joebowen/arduino_altimeter/Schematic&Boards/Joe's NonPyro Altimeter/Finished/arduino_schematic_with_ADXL377_without_pyro_etch_copper_bottom.pdf

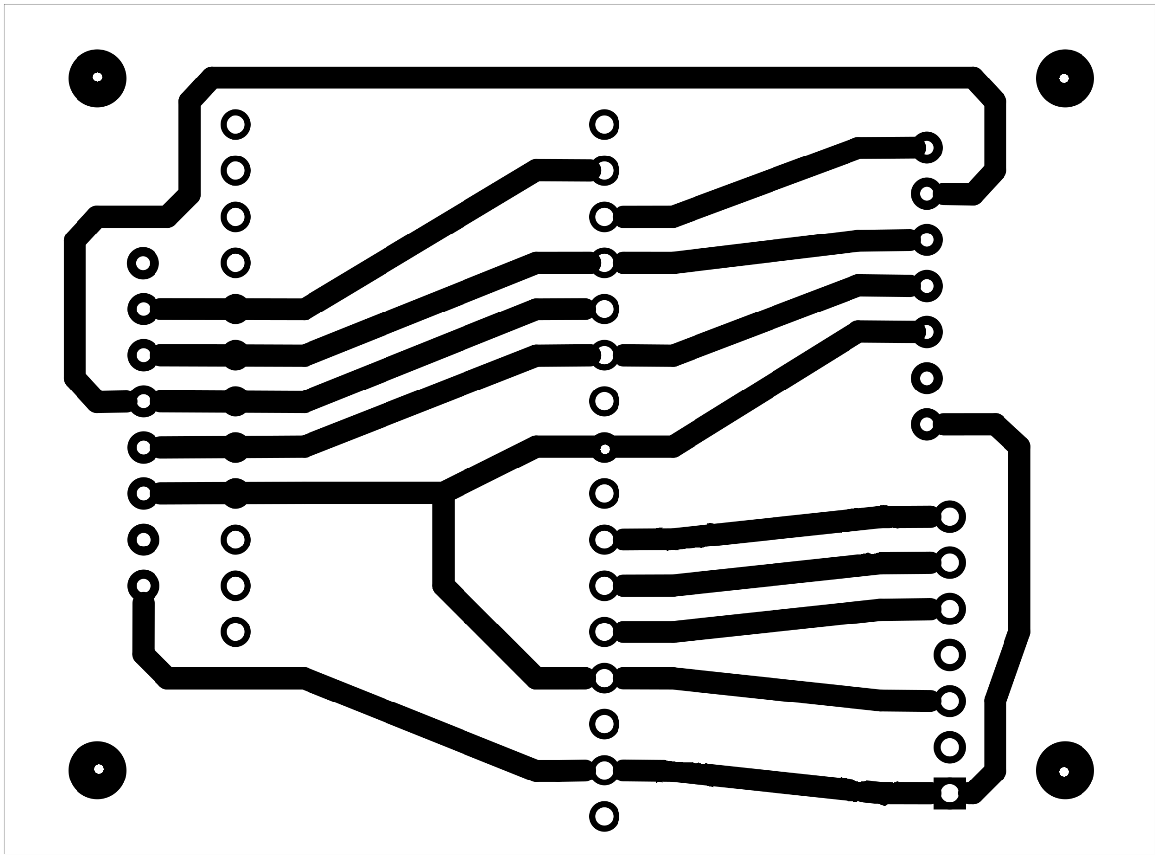
[picture p1: page 1]
