joebowen/arduino_altimeter/Schematic&Boards/Dan's Altimeter/arduino_schematic_etch_silk_bottom.pdf

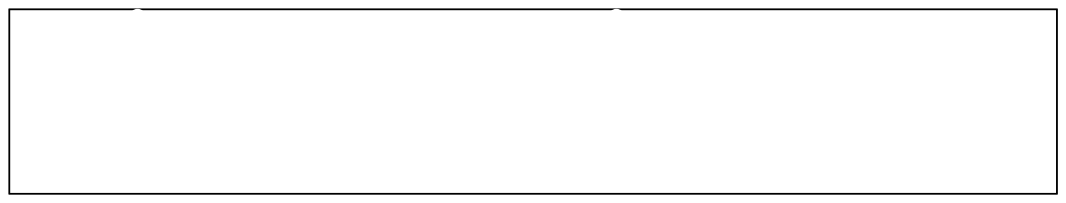
[picture p13: page 1]
