joebowen/arduino_altimeter/Schematic&Boards/Dan's Altimeter/arduino_schematic_etch_silk_bottom_mirror.pdf

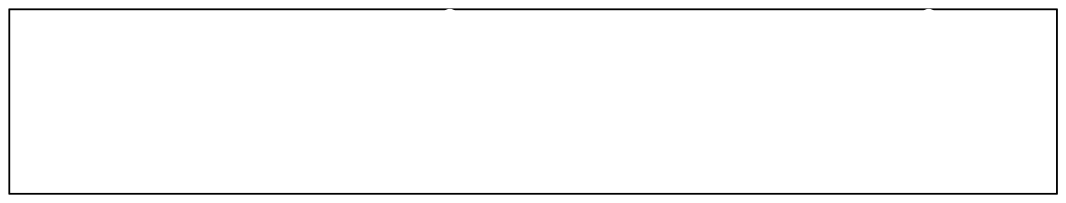
[picture p14: page 1]
