joebowen/arduino_altimeter/Schematic&Boards/Dan's Altimeter/arduino_schematic_etch_silk_top.pdf

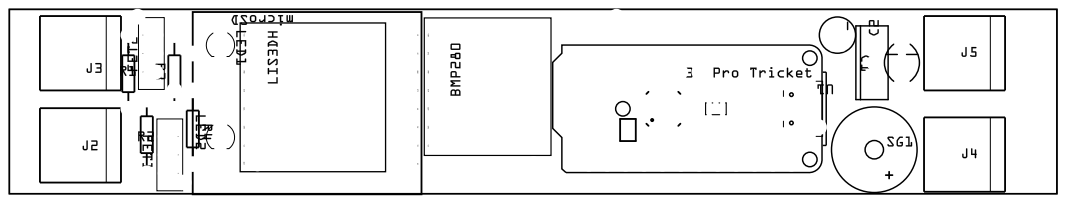
[picture p15: page 1]
