joebowen/arduino_altimeter/Schematic&Boards/Dan's Altimeter/arduino_schematic_etch_silk_top_mirror.pdf

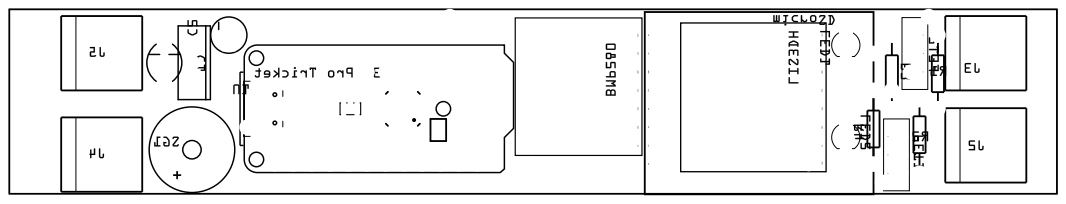
[picture p16: page 1]
