joebowen/arduino_altimeter/Schematic&Boards/Joe's Altimeter/arduino_schematic_with_ADXL377_etch_copper_bottom.pdf

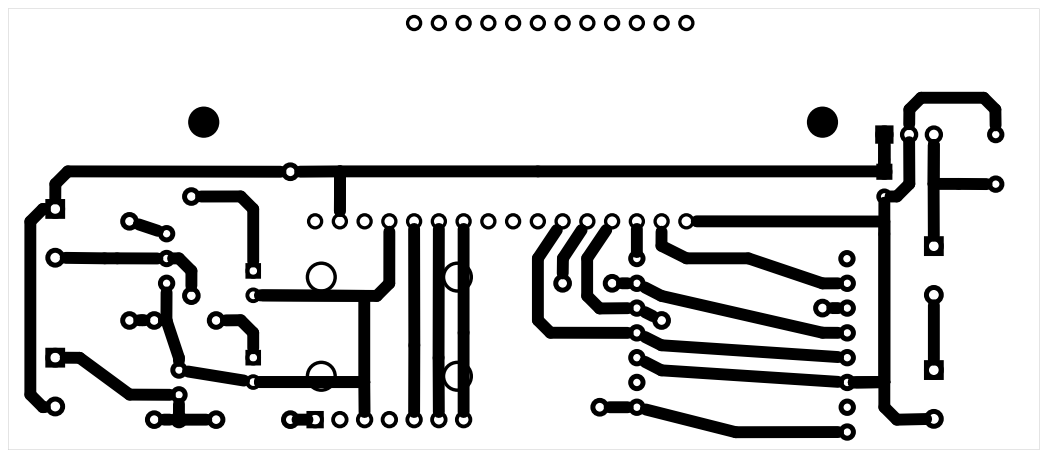
[picture p17: page 1]
