joebowen/arduino_altimeter/Schematic&Boards/Joe's Altimeter/arduino_schematic_with_ADXL377_etch_copper_bottom_mirror.pdf

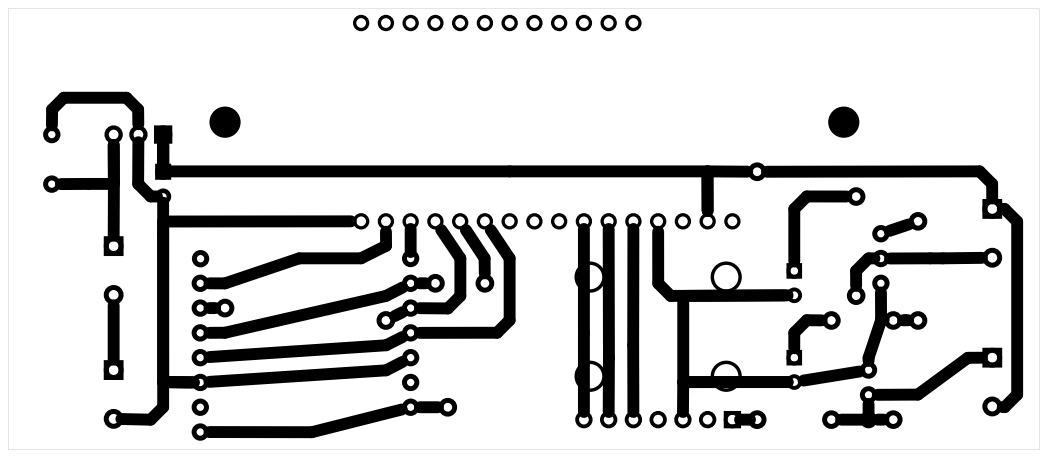
[picture p18: page 1]
