joebowen/arduino_altimeter/Schematic&Boards/Joe's Altimeter/arduino_schematic_with_ADXL377_etch_copper_top.pdf

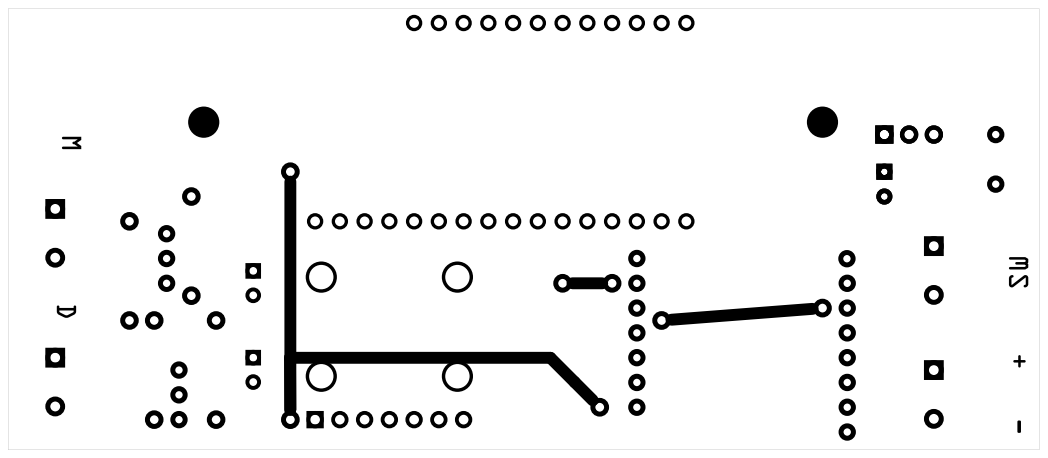
[picture p19: page 1]
