joebowen/arduino_altimeter/Schematic&Boards/Joe's Altimeter/arduino_schematic_with_ADXL377_etch_copper_top_mirror.pdf

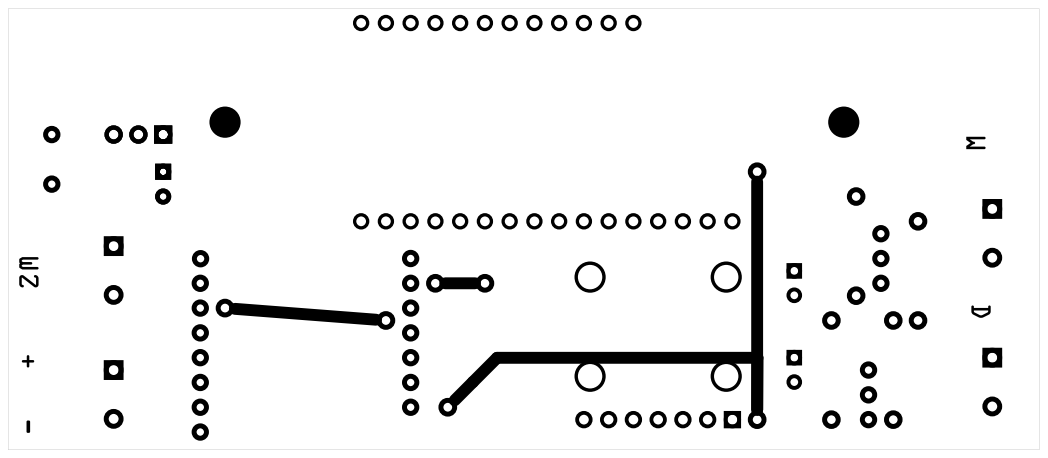
[picture p20: page 1]
