joebowen/arduino_altimeter/Schematic&Boards/Joe's Altimeter/arduino_schematic_with_ADXL377_etch_mask_bottom.pdf

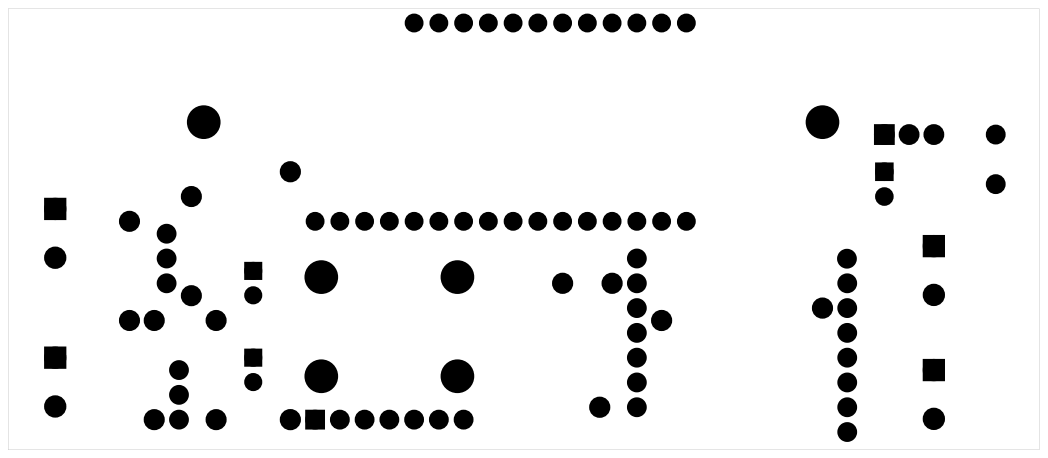
[picture p21: page 1]
