joebowen/arduino_altimeter/Schematic&Boards/Joe's Altimeter/arduino_schematic_with_ADXL377_etch_mask_bottom_mirror.pdf

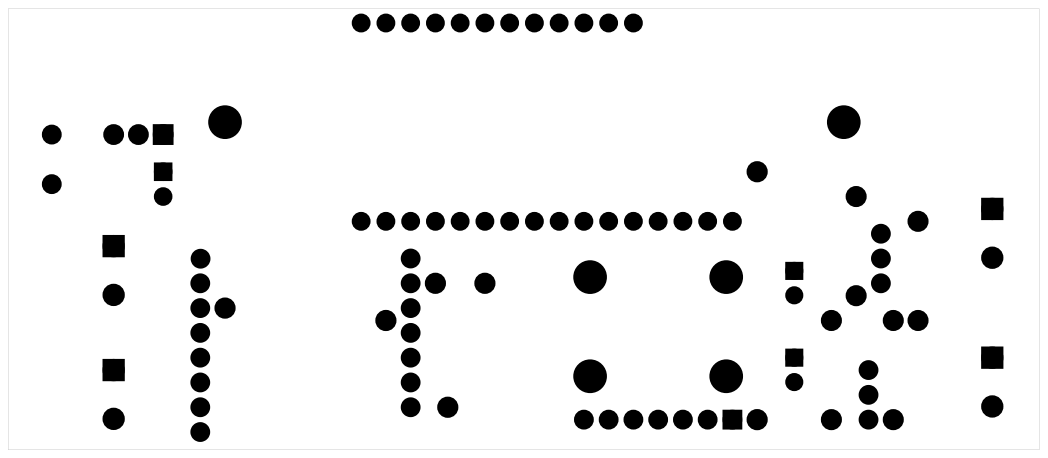
[picture p22: page 1]
