joebowen/arduino_altimeter/Schematic&Boards/Joe's Altimeter/arduino_schematic_with_ADXL377_etch_mask_top_mirror.pdf

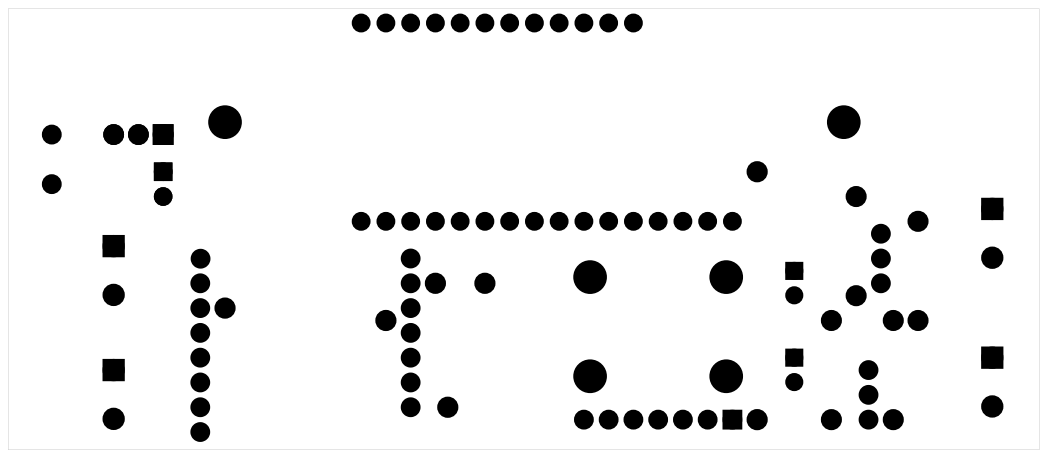
[picture p24: page 1]
