joebowen/arduino_altimeter/Schematic&Boards/Joe's Altimeter/arduino_schematic_with_ADXL377_etch_silk_bottom.pdf

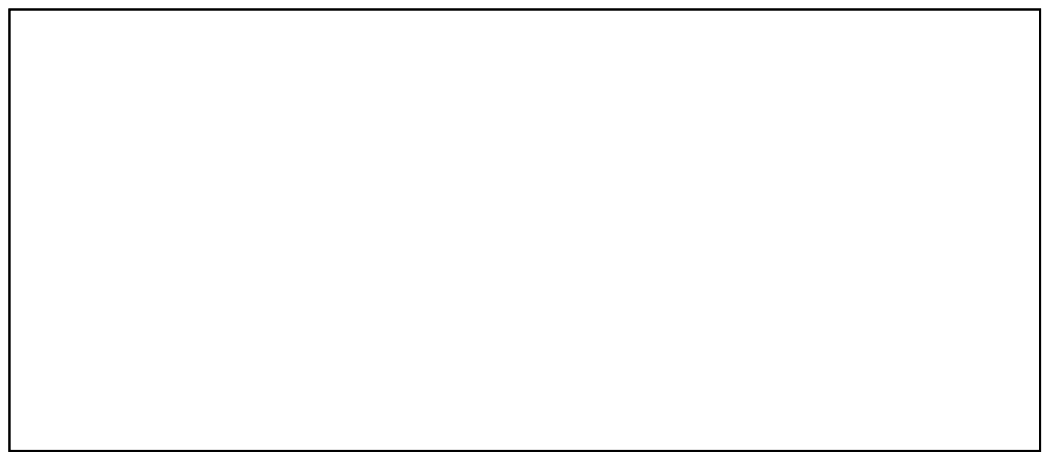
[picture p25: page 1]
