joebowen/arduino_altimeter/Schematic&Boards/Joe's Altimeter/arduino_schematic_with_ADXL377_etch_silk_bottom_mirror.pdf

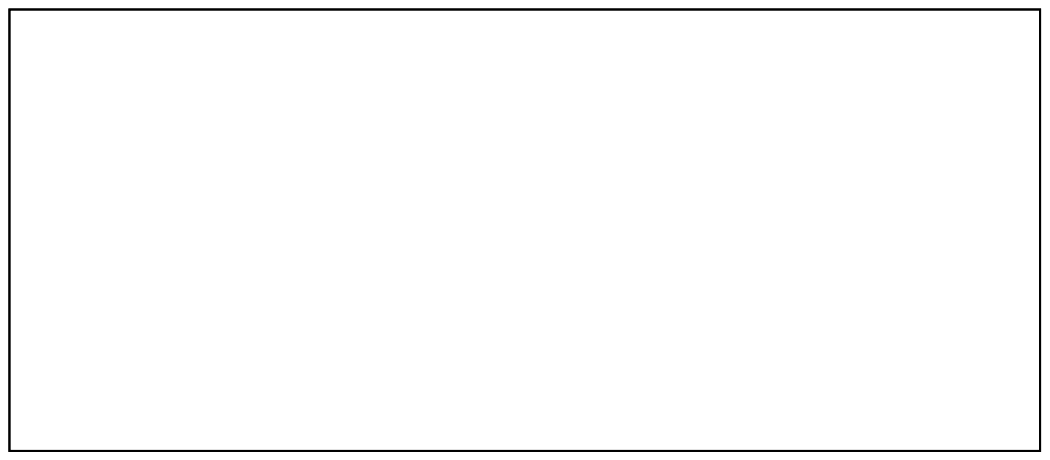
[picture p26: page 1]
