joebowen/arduino_altimeter/Schematic&Boards/Joe's Altimeter/arduino_schematic_with_ADXL377_etch_silk_top_mirror.pdf

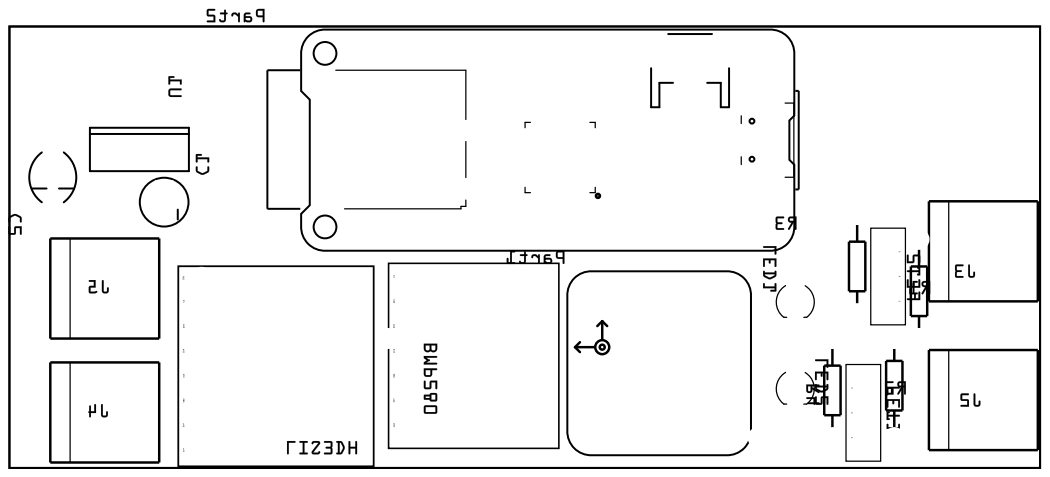
[picture p28: page 1]
