joebowen/arduino_altimeter/Schematic&Boards/Joe's NonPyro Altimeter/arduino_schematic_with_ADXL377_without_pyro_etch_copper_bottom.pdf

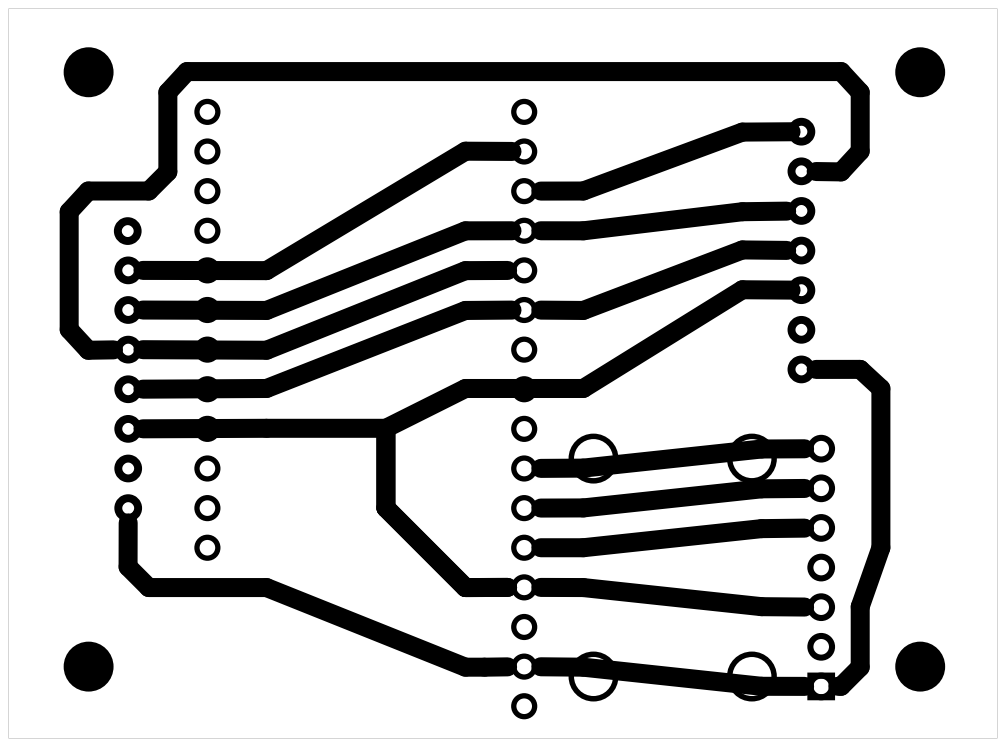
[picture p29: page 1]
