joebowen/arduino_altimeter/Schematic&Boards/Joe's NonPyro Altimeter/arduino_schematic_with_ADXL377_without_pyro_etch_copper_top.pdf

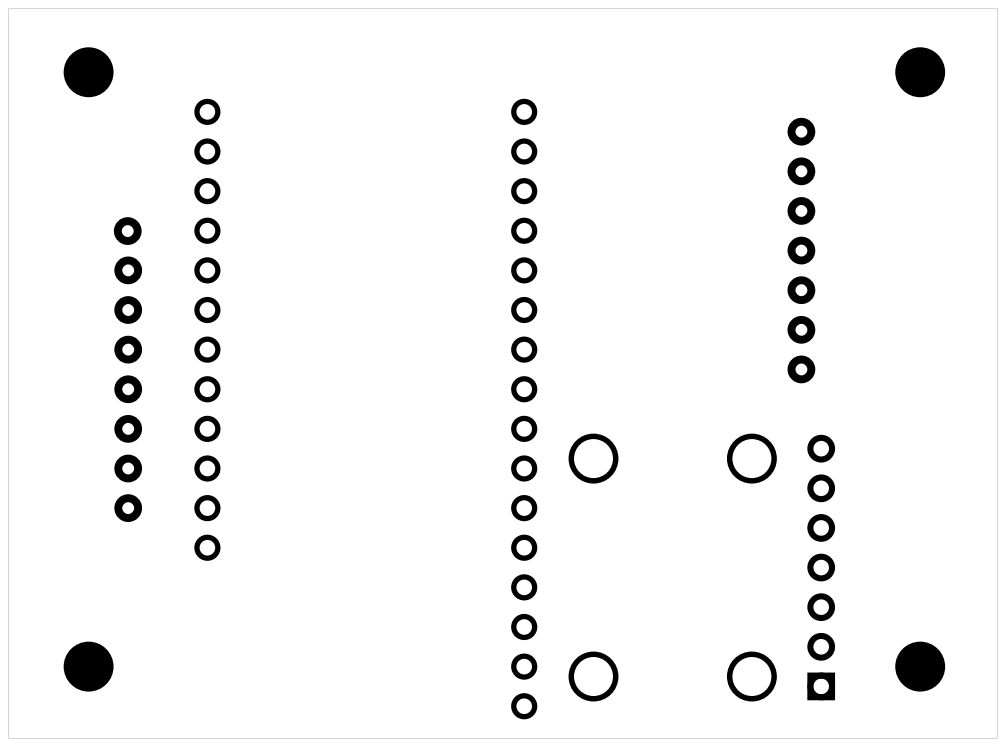
[picture p31: page 1]
