joebowen/arduino_altimeter/Schematic&Boards/Joe's NonPyro Altimeter/arduino_schematic_with_ADXL377_without_pyro_etch_copper_top_mirror.pdf

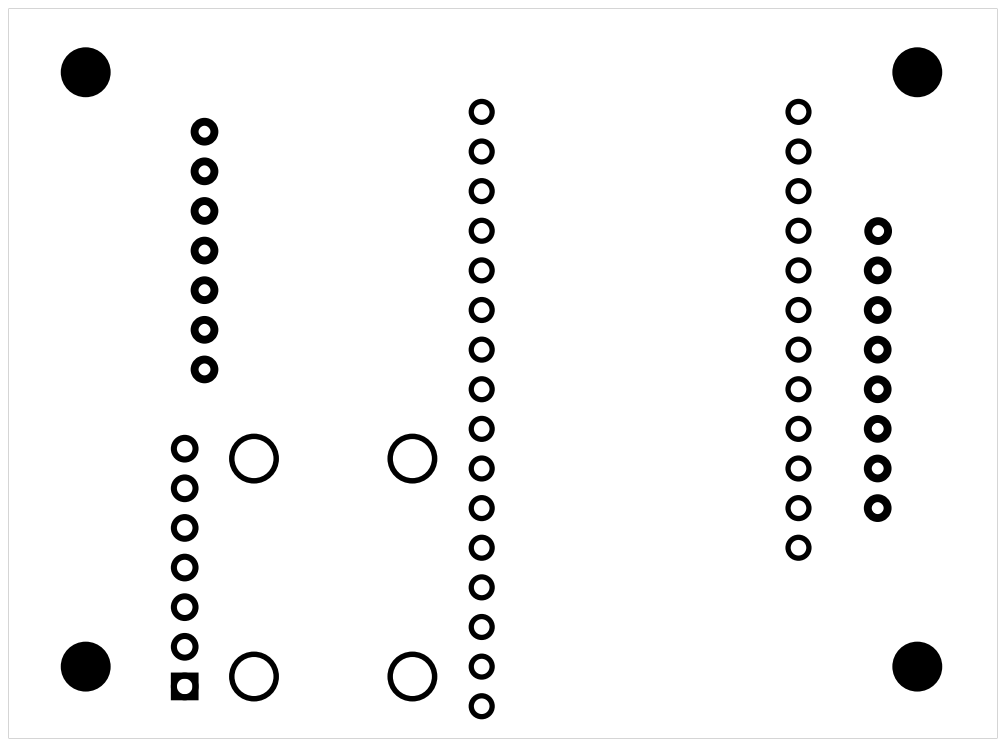
[picture p32: page 1]
