joebowen/arduino_altimeter/Schematic&Boards/Altimeter-baro-only/altimeter_baro_only_etch_copper_bottom.pdf

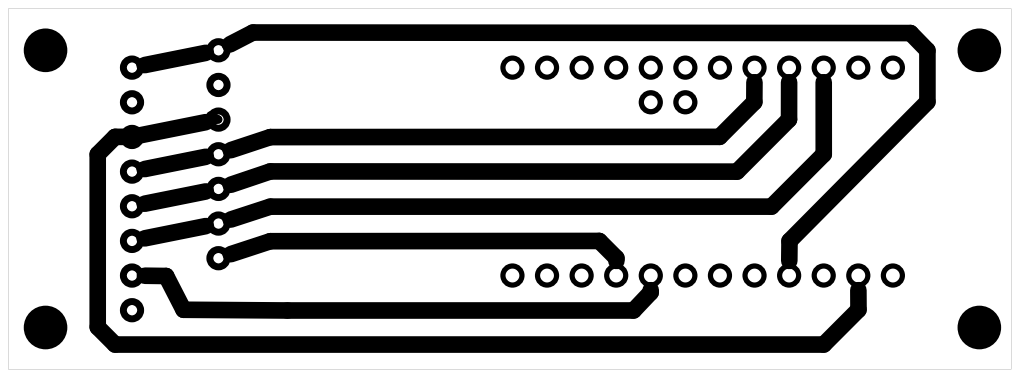
[picture p39: page 1]
