joebowen/arduino_altimeter/Schematic&Boards/Altimeter-baro-only/altimeter_baro_only_etch_copper_bottom_mirror.pdf

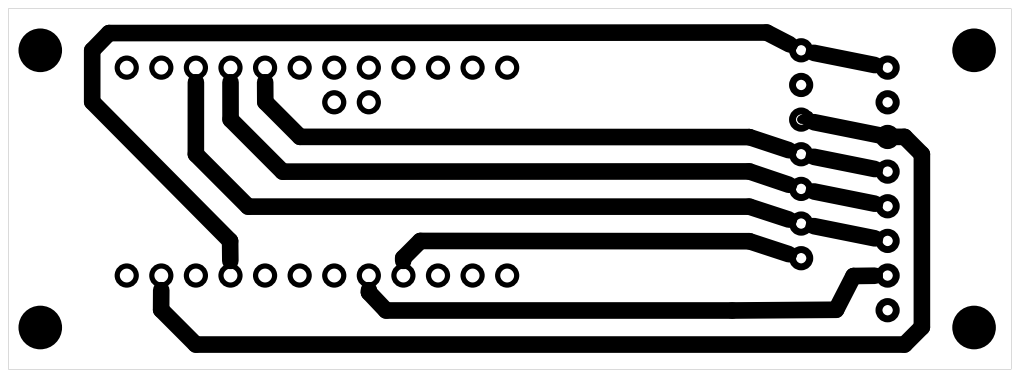
[picture p40: page 1]
