joebowen/arduino_altimeter/Schematic&Boards/Altimeter-baro-only/altimeter_baro_only_etch_copper_top.pdf

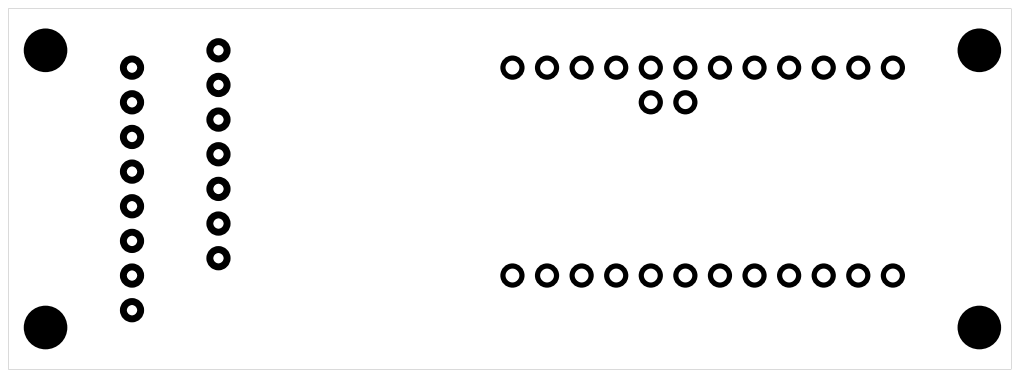
[picture p41: page 1]
