joebowen/arduino_altimeter/Schematic&Boards/Altimeter-baro-only/altimeter_baro_only_etch_copper_top_mirror.pdf

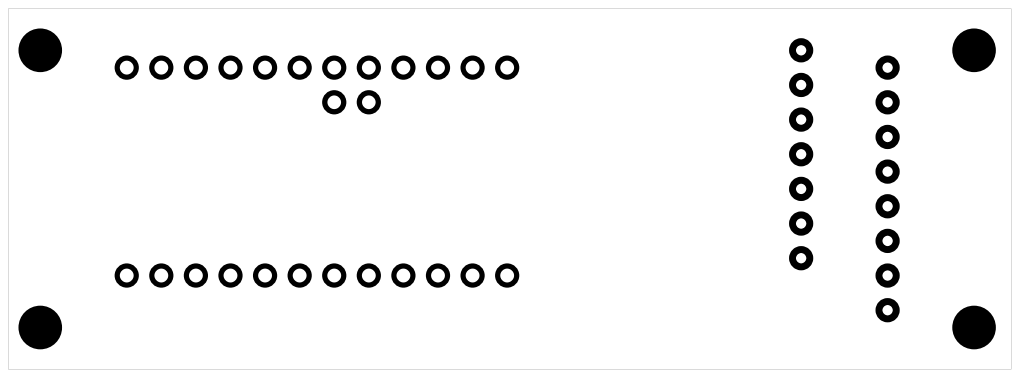
[picture p42: page 1]
