joebowen/arduino_altimeter/Schematic&Boards/Altimeter-baro-only/altimeter_baro_only_etch_mask_bottom.pdf

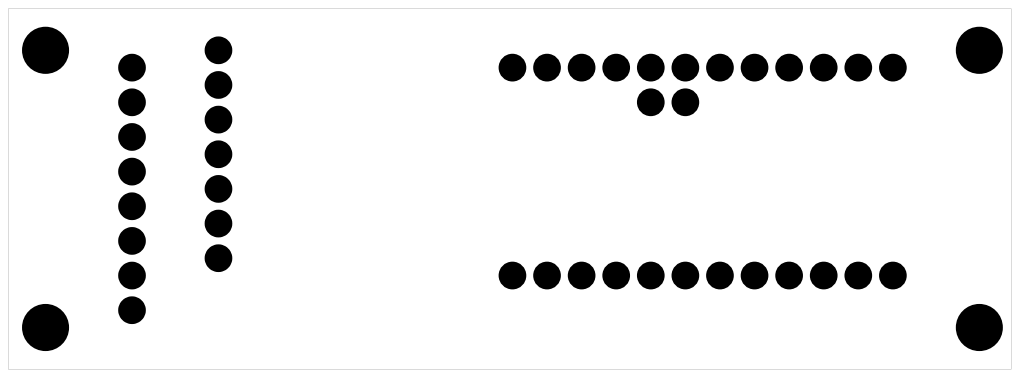
[picture p43: page 1]
