joebowen/arduino_altimeter/Schematic&Boards/Altimeter-baro-only/altimeter_baro_only_etch_mask_bottom_mirror.pdf

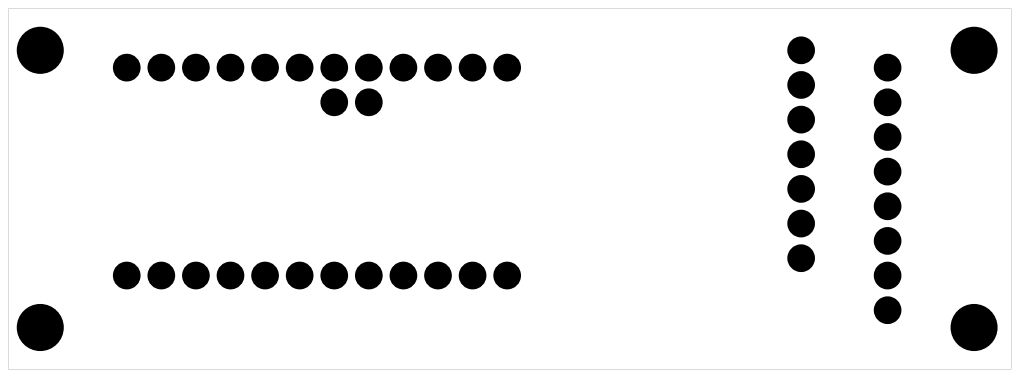
[picture p44: page 1]
