joebowen/arduino_altimeter/Schematic&Boards/Altimeter-baro-only/altimeter_baro_only_etch_silk_bottom.pdf

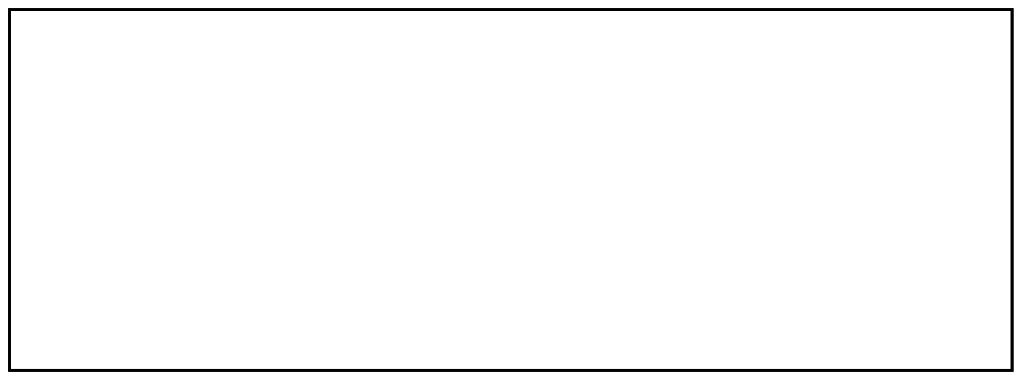
[picture p45: page 1]
