joebowen/arduino_altimeter/Schematic&Boards/Altimeter-baro-only/altimeter_baro_only_etch_silk_bottom_mirror.pdf

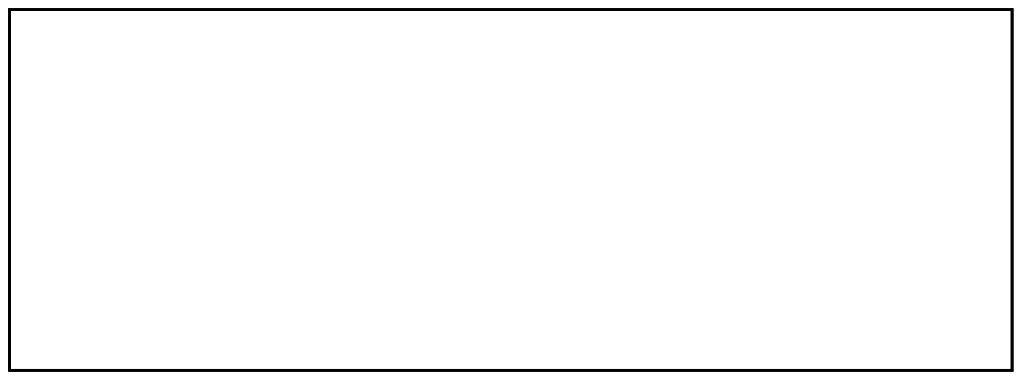
[picture p46: page 1]
