joebowen/arduino_altimeter/Schematic&Boards/Altimeter-baro-only/altimeter_baro_only_etch_silk_top.pdf

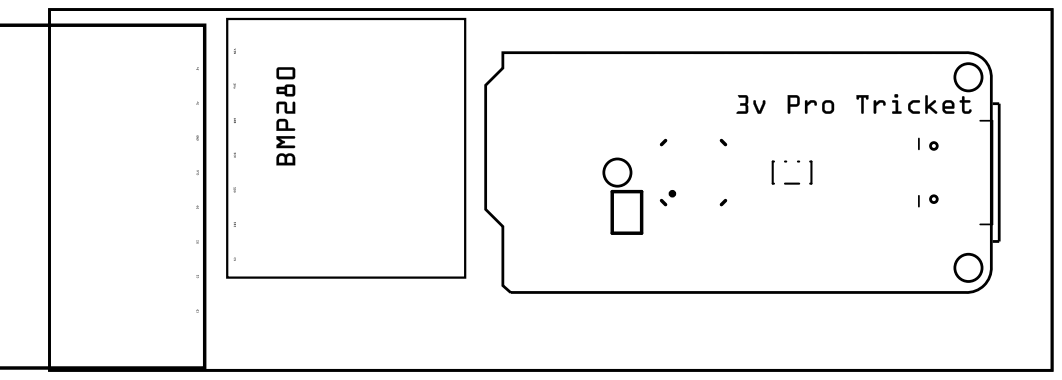
[picture p47: page 1]
