joebowen/arduino_altimeter/Schematic&Boards/Altimeter-baro-only/altimeter_baro_only_etch_silk_top_mirror.pdf

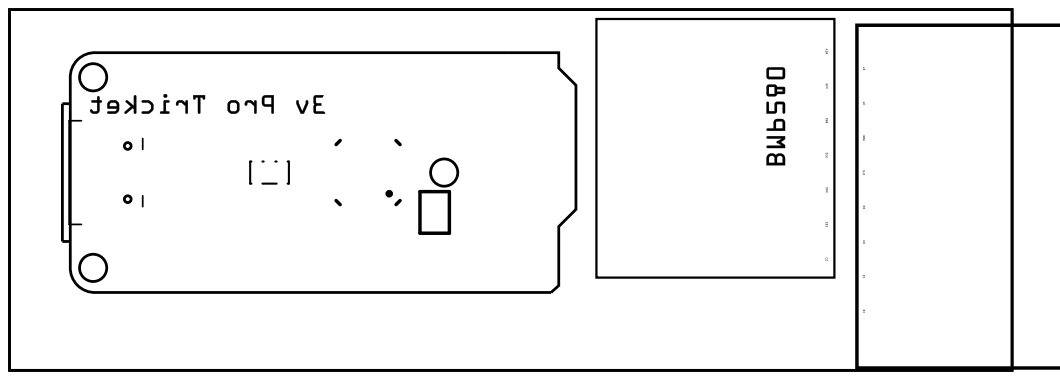
[picture p48: page 1]
