joebowen/arduino_altimeter/Schematic&Boards/Altimeter-baro-only/altimeter_baro_only_pcb.pdf

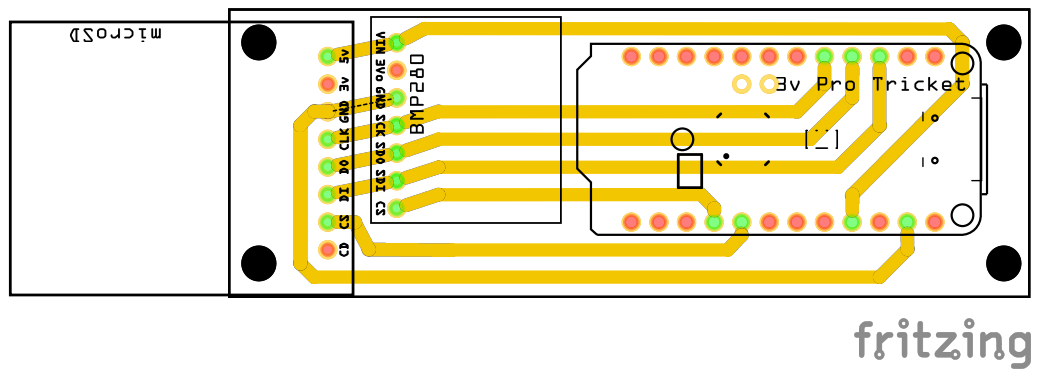
[picture p49: page 1]
