joebowen/arduino_altimeter/Schematic&Boards/PyroCircuit/PyroCircuit_etch_copper_bottom.pdf

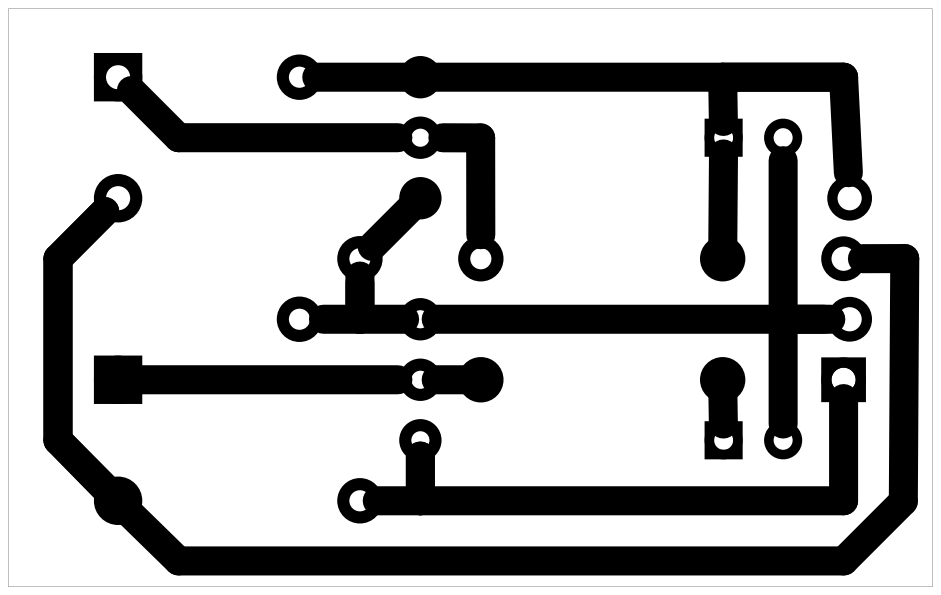
[picture p50: page 1]
