joebowen/arduino_altimeter/Schematic&Boards/PyroCircuit/PyroCircuit_etch_copper_bottom_mirror.pdf

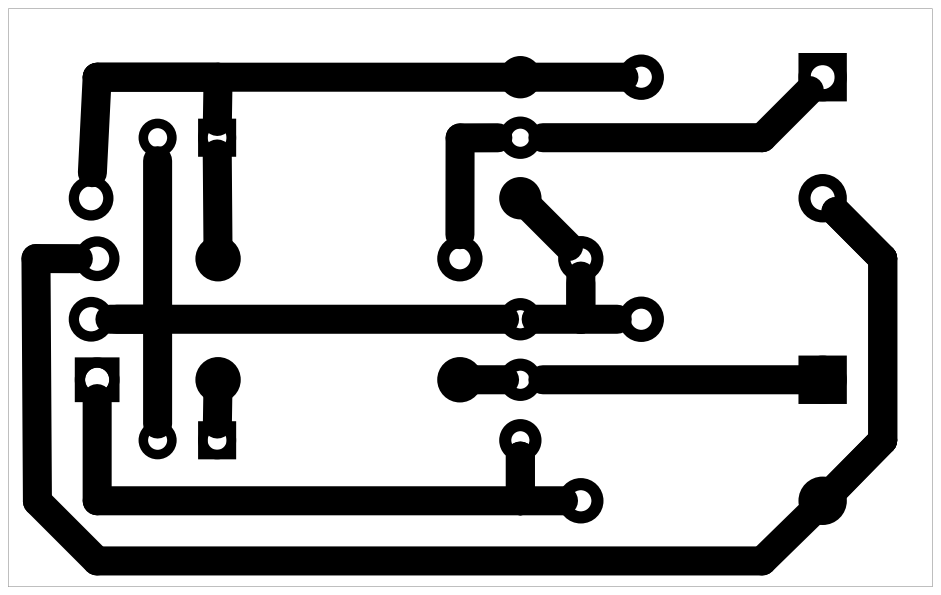
[picture p51: page 1]
