joebowen/arduino_altimeter/Schematic&Boards/PyroCircuit/PyroCircuit_etch_mask_bottom.pdf

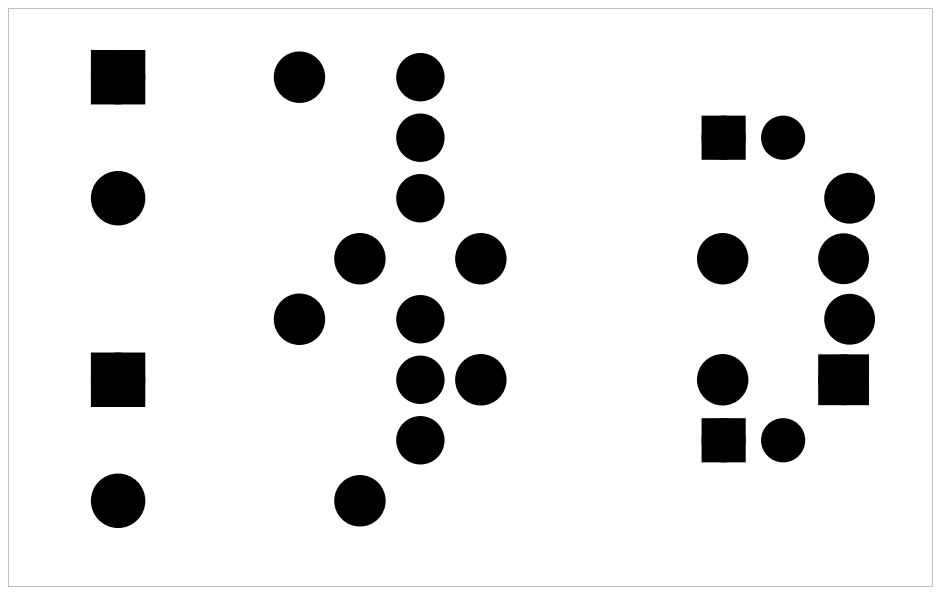
[picture p52: page 1]
