joebowen/arduino_altimeter/Schematic&Boards/PyroCircuit/PyroCircuit_etch_mask_bottom_mirror.pdf

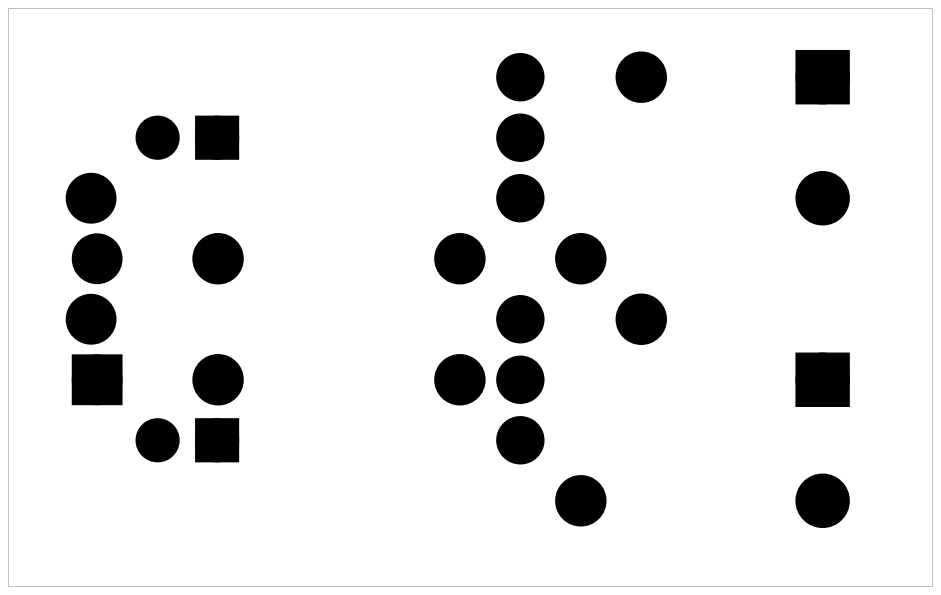
[picture p53: page 1]
