joebowen/arduino_altimeter/Schematic&Boards/PyroCircuit/PyroCircuit_etch_silk_bottom.pdf

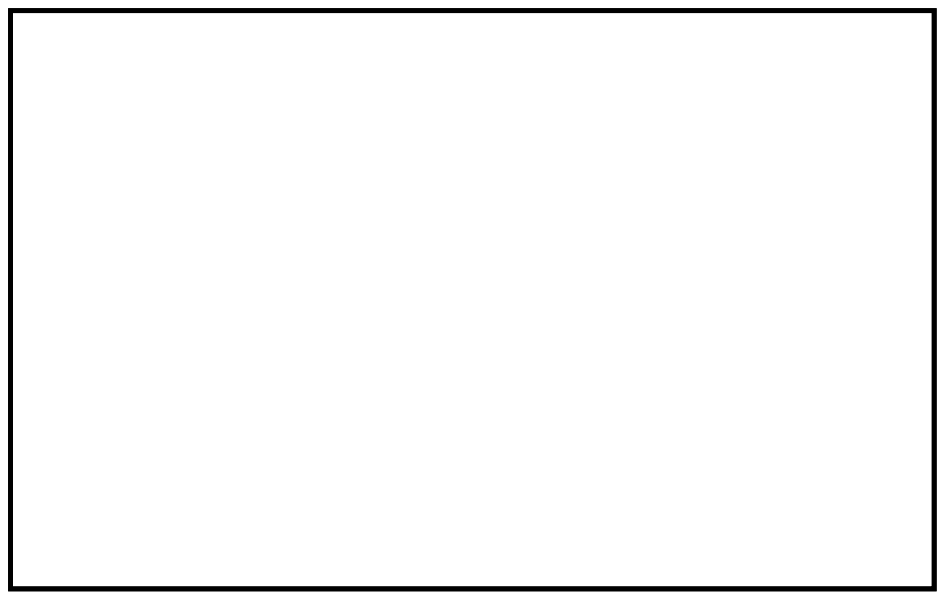
[picture p54: page 1]
