joebowen/arduino_altimeter/Schematic&Boards/PyroCircuit/PyroCircuit_etch_silk_bottom_mirror.pdf

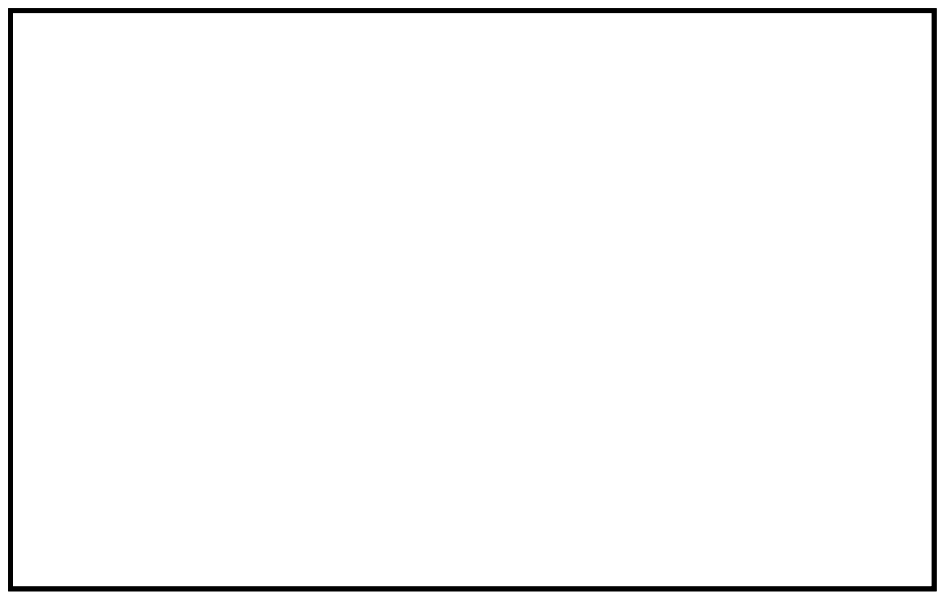
[picture p55: page 1]
